jessehamner/AtariPunkConsole/graphics/asteroids.bmp

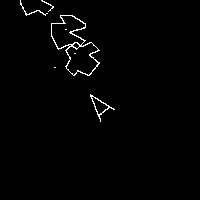
graphics/asteroids.bmp
